iAmGroute/HS100R/Rev0A/HS100R ADC Graphs/cap and res 2.png

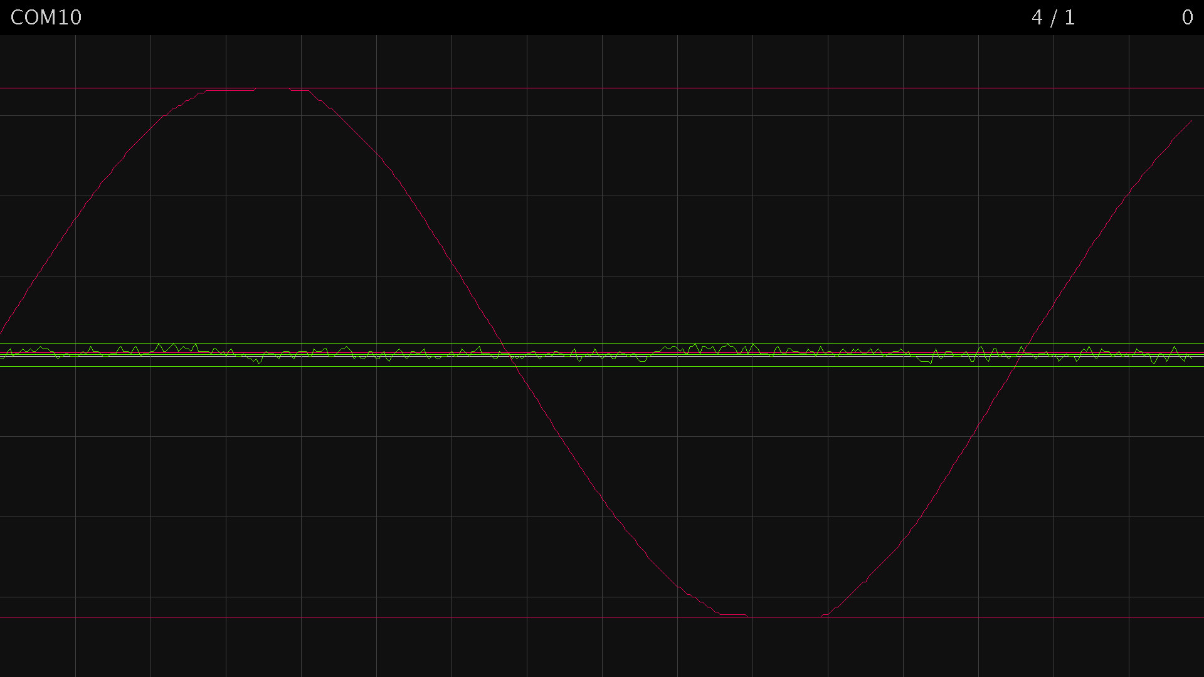
Rev0A/HS100R ADC Graphs/cap and res 2.png
