iAmGroute/HS100R/Rev0A/HS100R ADC Graphs/no trim max gain 8 bit 2.png

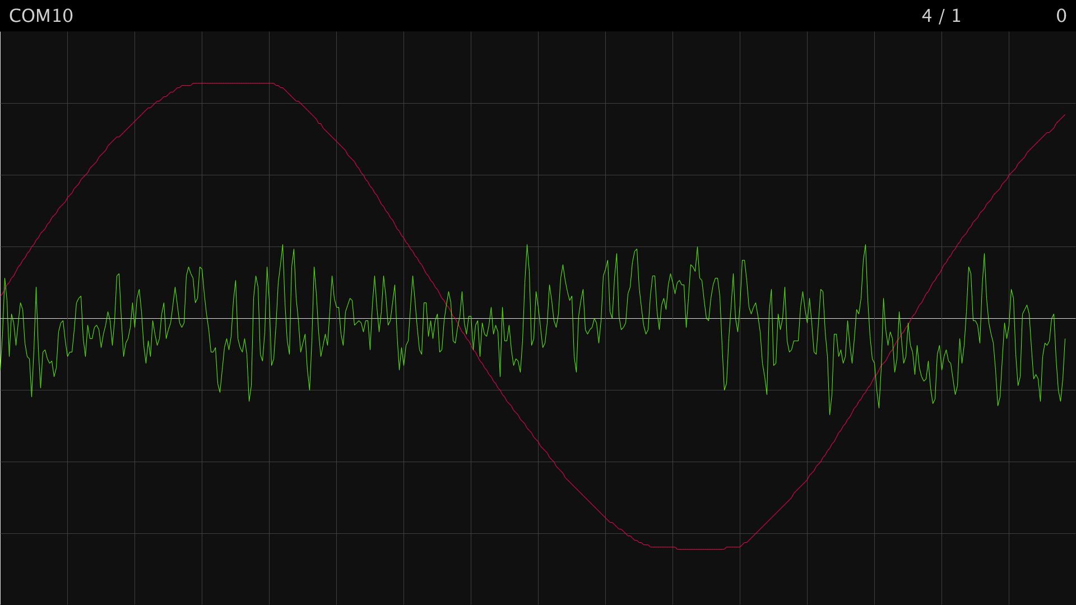
Rev0A/HS100R ADC Graphs/no trim max gain 8 bit 2.png
