iAmGroute/HS100R/Rev0A/HS100R ADC Graphs/no trim max gain 10 bit 1.png

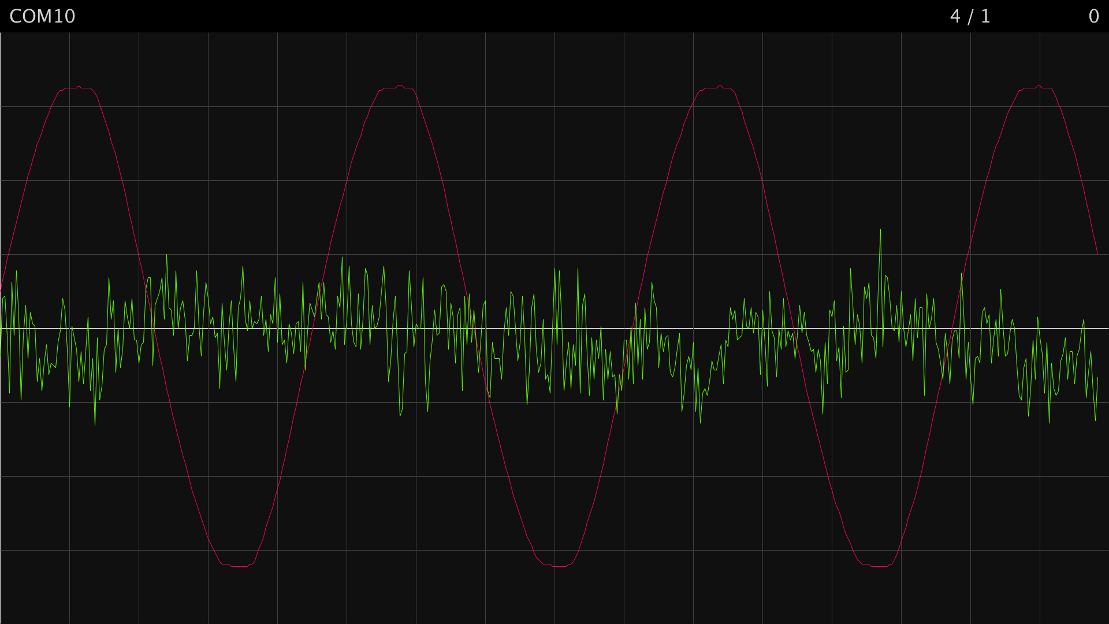
Rev0A/HS100R ADC Graphs/no trim max gain 10 bit 1.png
