iAmGroute/HS100R/Rev0A/HS100R ADC Graphs/test0.png

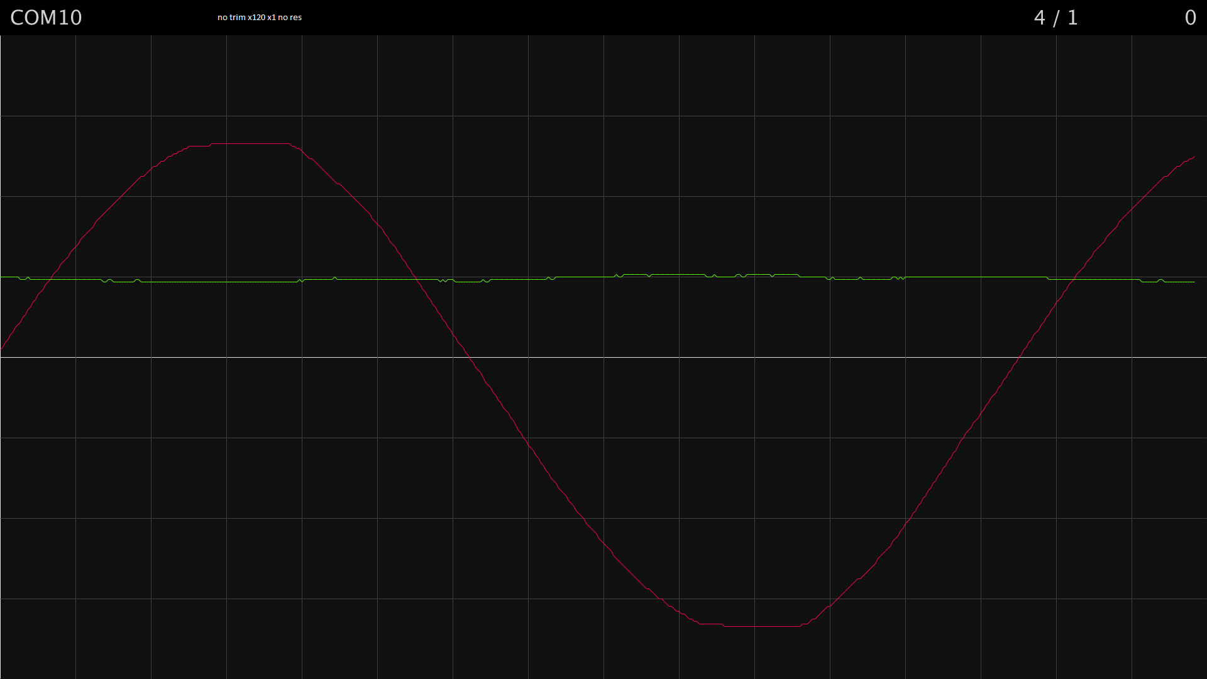
Rev0A/HS100R ADC Graphs/test0.png
