iAmGroute/HS100R/Rev0A/HS100R ADC Graphs/test1.png

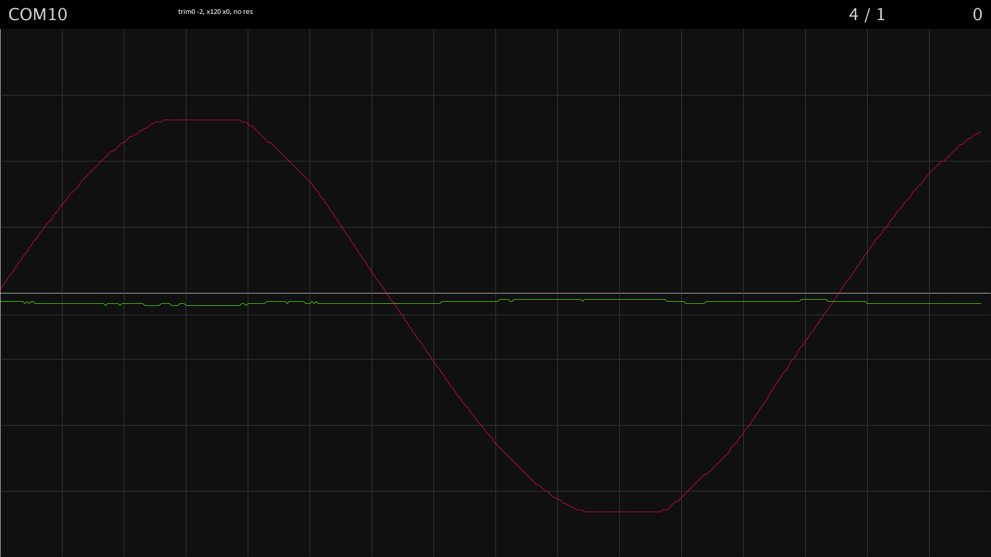
Rev0A/HS100R ADC Graphs/test1.png
